Gloeidraad/AMFM-modulator-with-ESP32-module/images/esp32-wrover-cam-front.jpeg

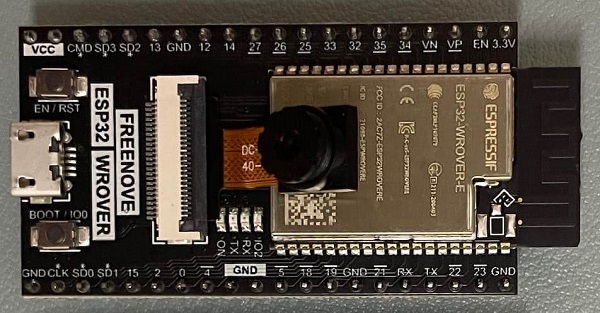
images/esp32-wrover-cam-front.jpeg
