Gloeidraad/AMFM-modulator-with-ESP32-module/V1.7/ASSY_1_7/3D-printables/Case Bezel Inner Half.jpg

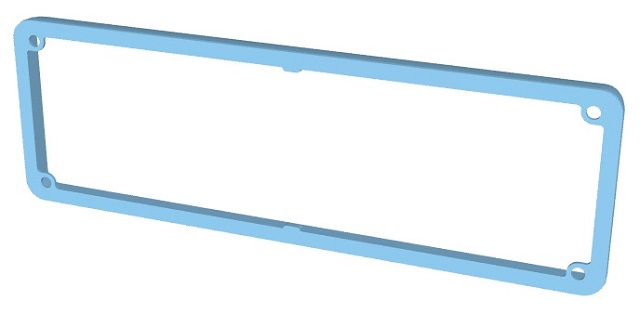
V1.7/ASSY_1_7/3D-printables/Case Bezel Inner Half.jpg
